airowl-iot/airowl/Firmware/squareline/projects/ui_square_line/cache/thumb_546388984Screenshot 2025-09-16 161635.png

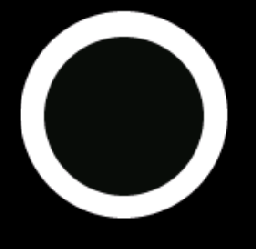
Firmware/squareline/projects/ui_square_line/cache/thumb_546388984Screenshot 2025-09-16 161635.png
