airowl-iot/airowl/Firmware/squareline/projects/ui_square_line/cache/thumb_812625368Glowing Blue Ring on Black.png

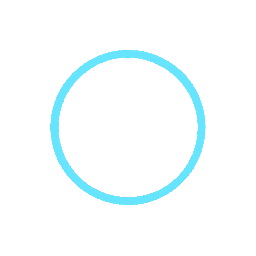
Firmware/squareline/projects/ui_square_line/cache/thumb_812625368Glowing Blue Ring on Black.png
