airowl-iot/airowl/Images/AIROWL edited renders and animation/n7.png

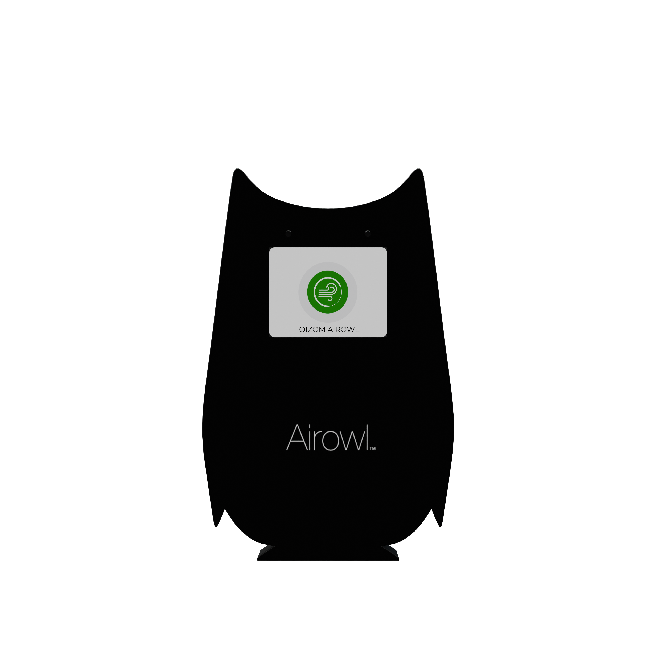
Images/AIROWL edited renders and animation/n7.png
