airowl-iot/airowl/Images/AIROWL edited renders and animation/n8.png

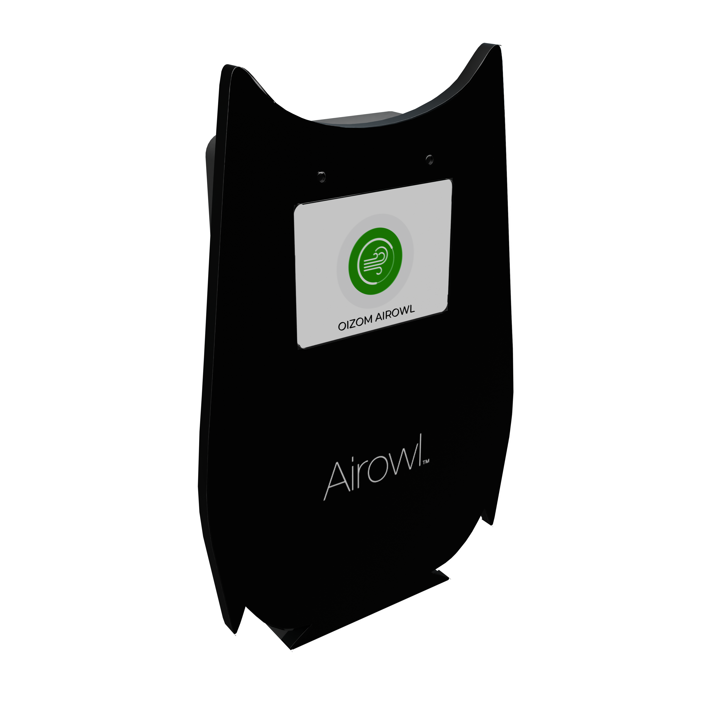
Images/AIROWL edited renders and animation/n8.png
