airowl-iot/airowl/Images/AIROWL edited renders and animation/n9.png

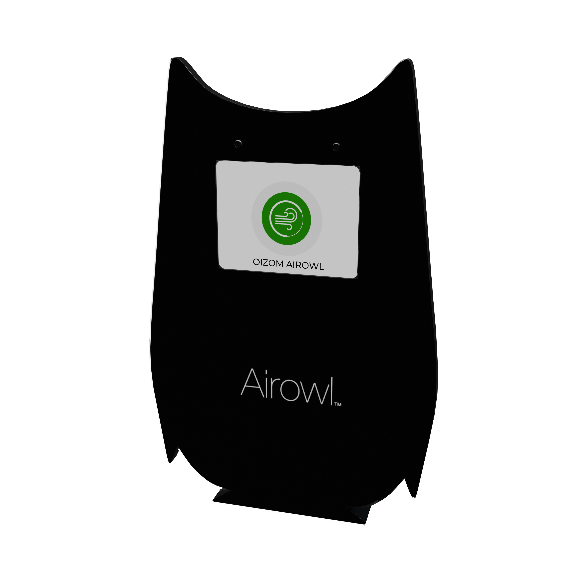
Images/AIROWL edited renders and animation/n9.png
