airowl-iot/airowl/Images/AIROWL edited renders and animation/n 1.n.png

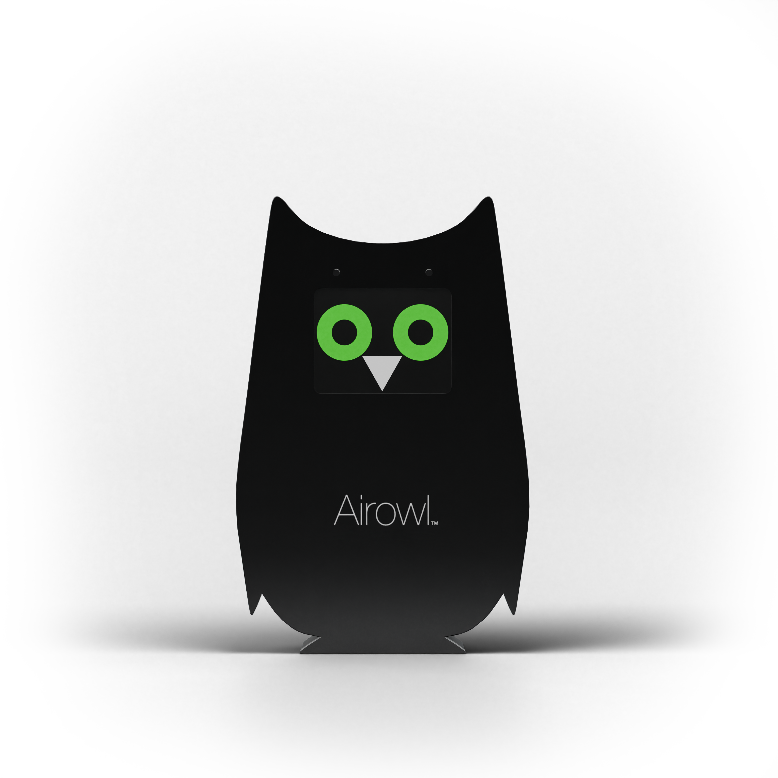
Images/AIROWL edited renders and animation/n 1.n.png
