airowl-iot/airowl/Images/AIROWL edited renders and animation/n 1.png

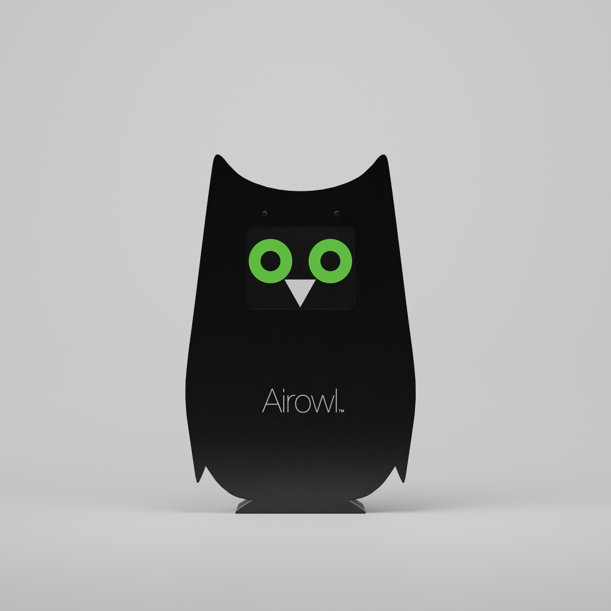
Images/AIROWL edited renders and animation/n 1.png
