airowl-iot/airowl/Images/AIROWL edited renders and animation/n 2.n.png

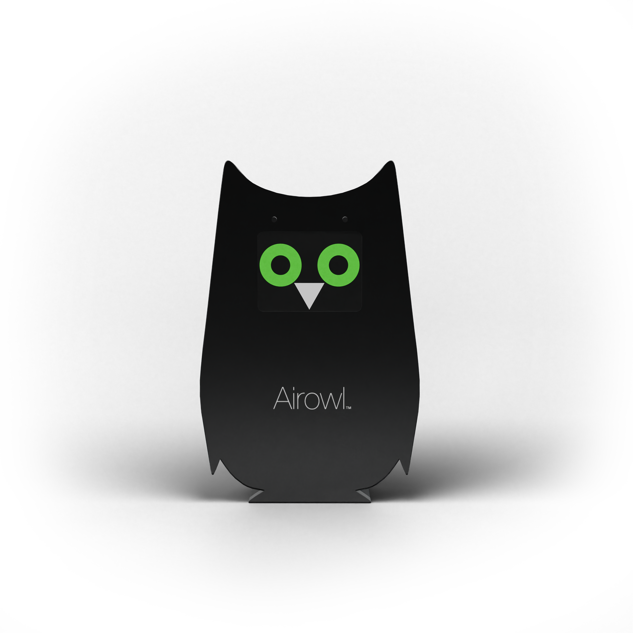
Images/AIROWL edited renders and animation/n 2.n.png
