airowl-iot/airowl/Images/AIROWL edited renders and animation/n 2e.png

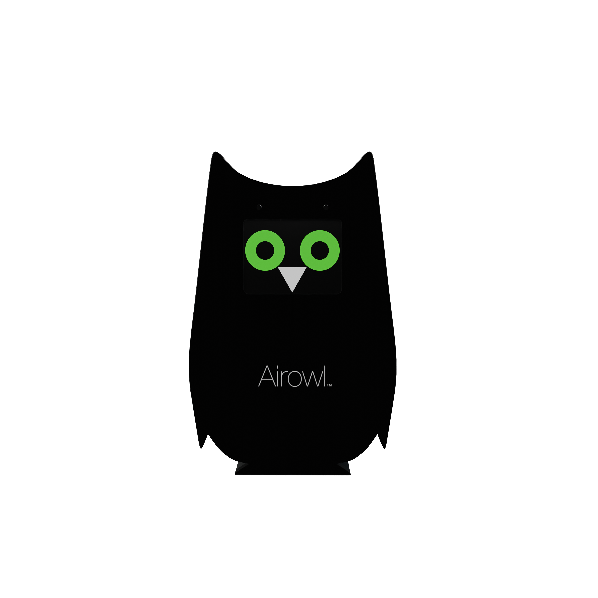
Images/AIROWL edited renders and animation/n 2e.png
