airowl-iot/airowl/Images/AIROWL edited renders and animation/n 3.n.png

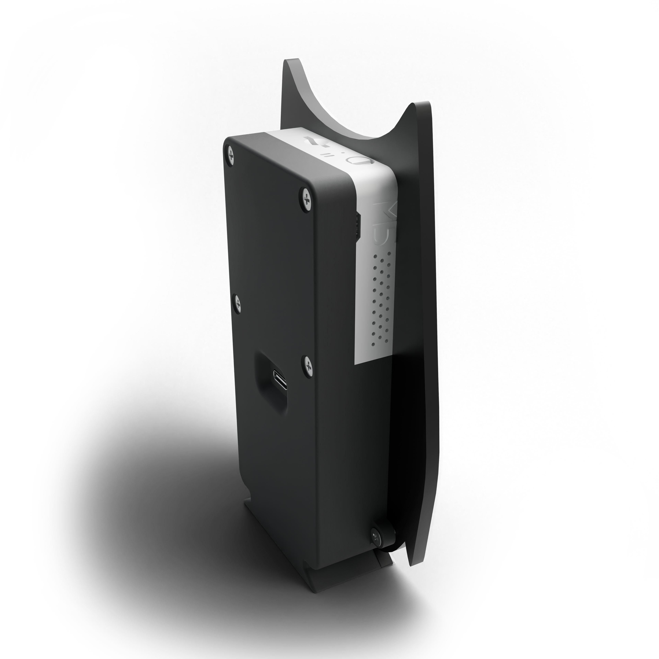
Images/AIROWL edited renders and animation/n 3.n.png
