airowl-iot/airowl/Images/AIROWL edited renders and animation/n 3e.png

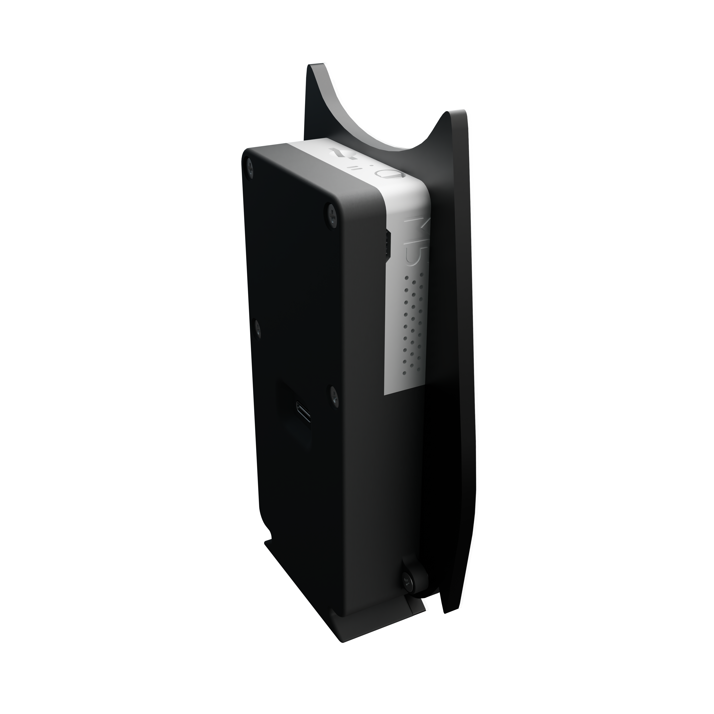
Images/AIROWL edited renders and animation/n 3e.png
