airowl-iot/airowl/Images/AIROWL edited renders and animation/n 4.n.png

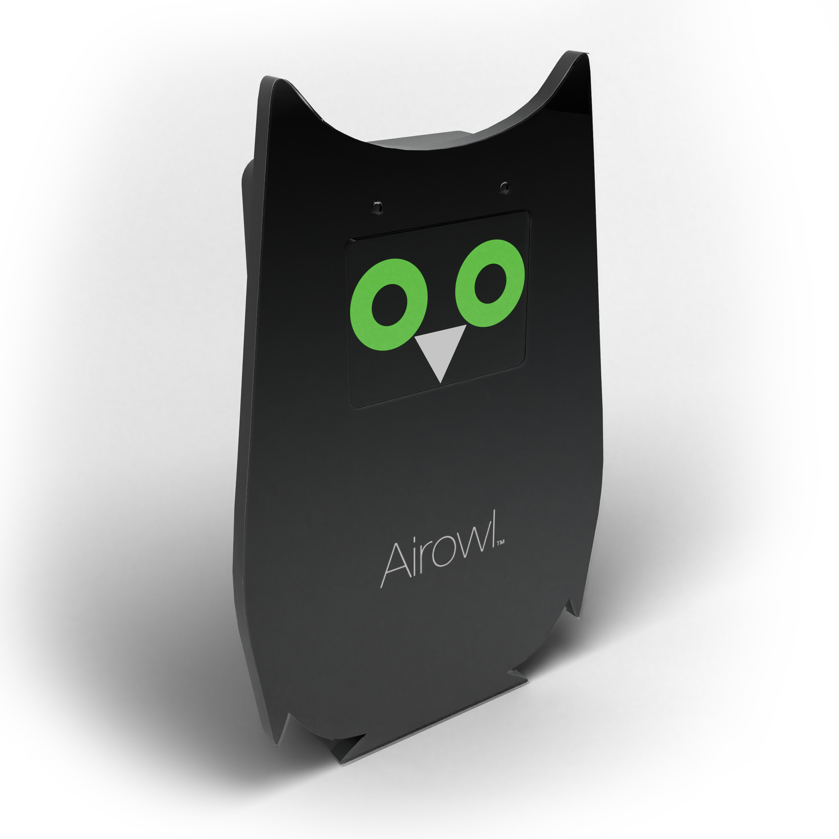
Images/AIROWL edited renders and animation/n 4.n.png
