airowl-iot/airowl/Images/AIROWL edited renders and animation/n 4.png

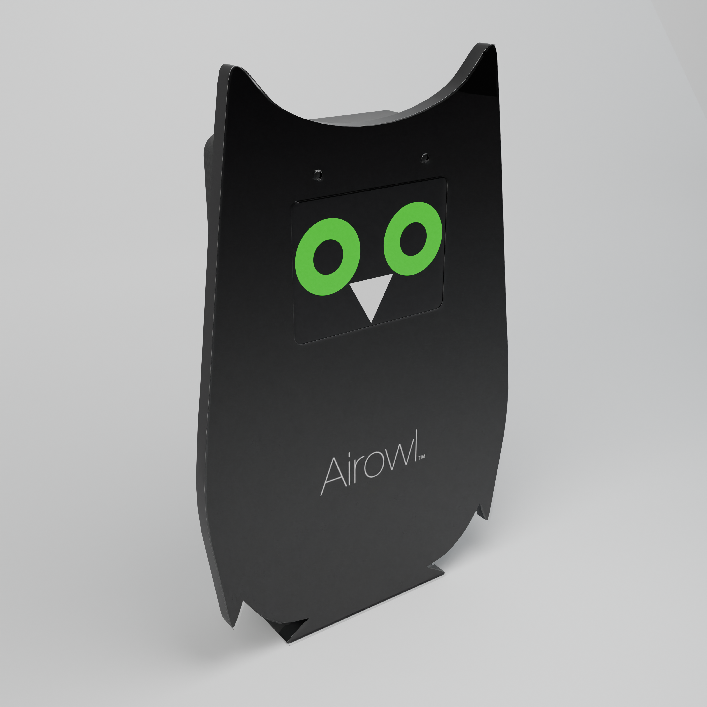
Images/AIROWL edited renders and animation/n 4.png
