airowl-iot/airowl/Images/AIROWL edited renders and animation/n 5.n.png

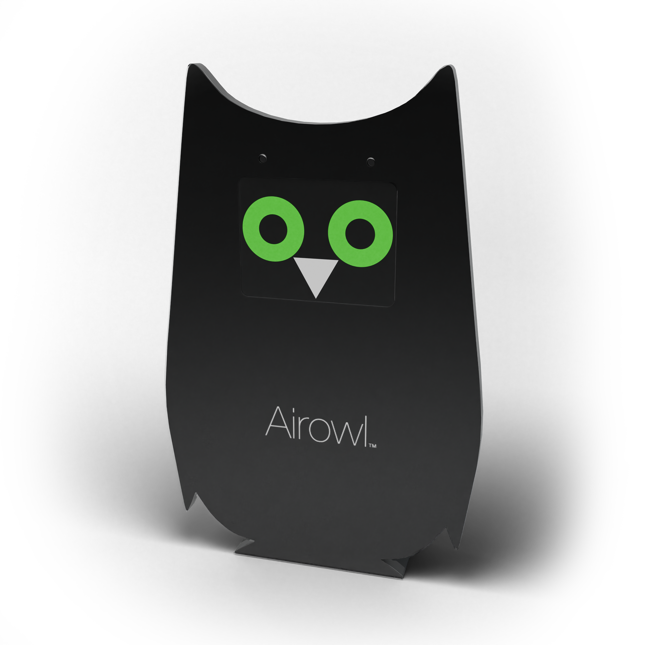
Images/AIROWL edited renders and animation/n 5.n.png
