airowl-iot/airowl/Images/AIROWL edited renders and animation/n 5.png

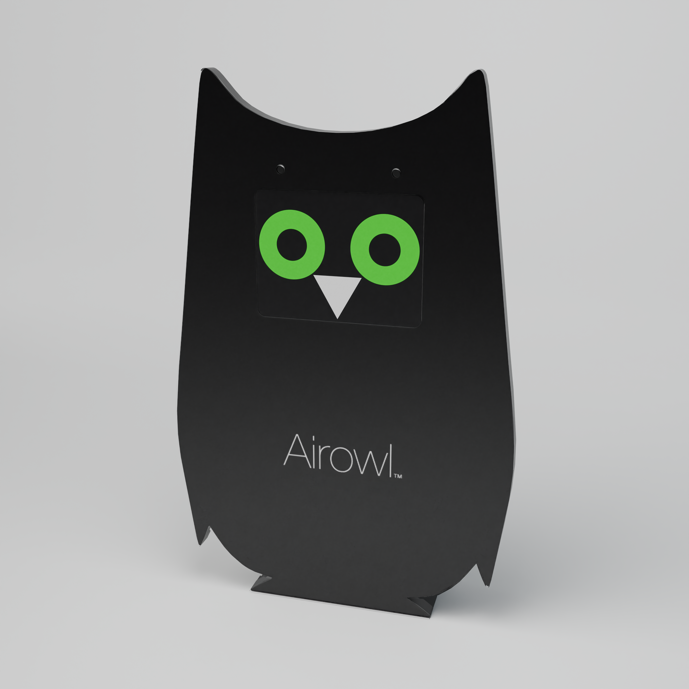
Images/AIROWL edited renders and animation/n 5.png
