airowl-iot/airowl/Images/AIROWL edited renders and animation/n 6.n.png

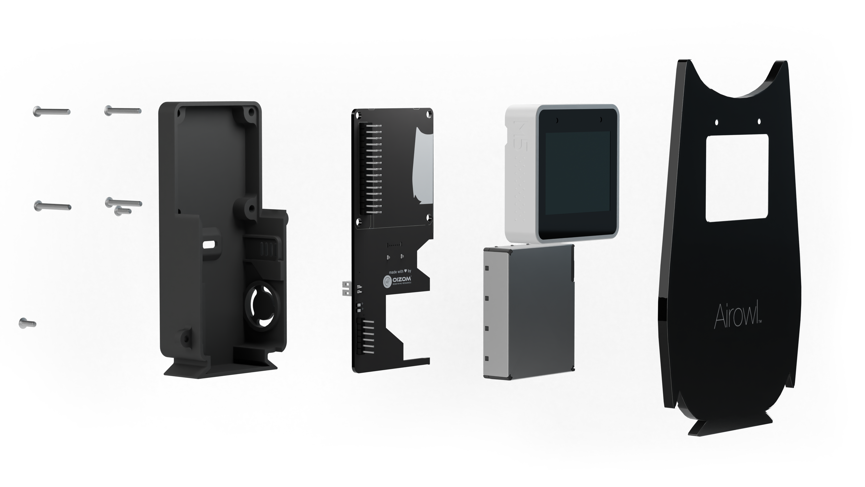
Images/AIROWL edited renders and animation/n 6.n.png
