airowl-iot/airowl/Images/AIROWL edited renders and animation/X1.png

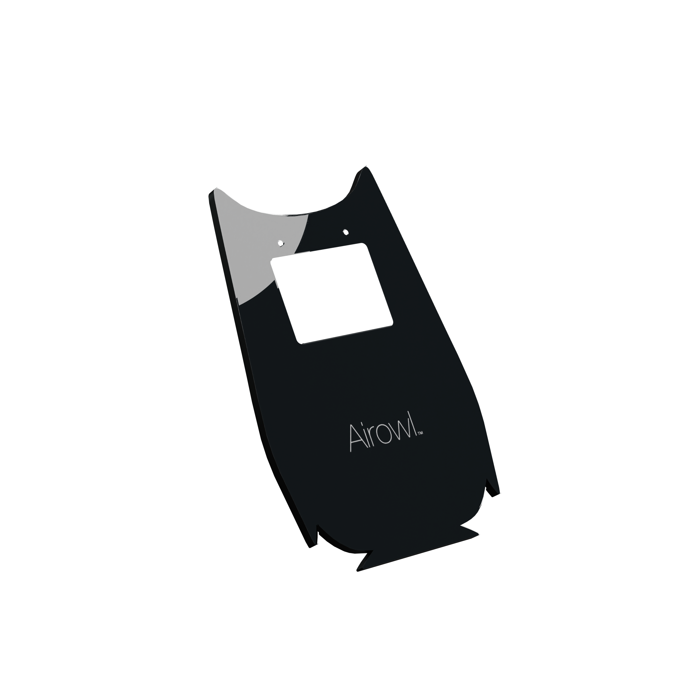
Images/AIROWL edited renders and animation/X1.png
