airowl-iot/airowl/Images/AIROWL edited renders and animation/x3.png

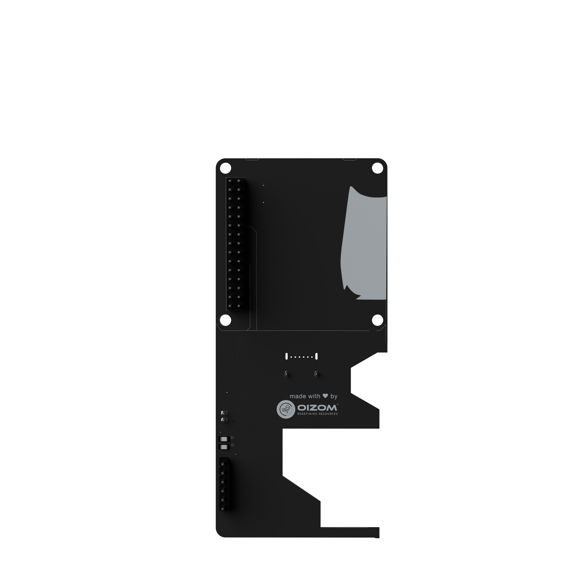
Images/AIROWL edited renders and animation/x3.png
