airowl-iot/airowl/Images/AIROWL edited renders and animation/x4.png

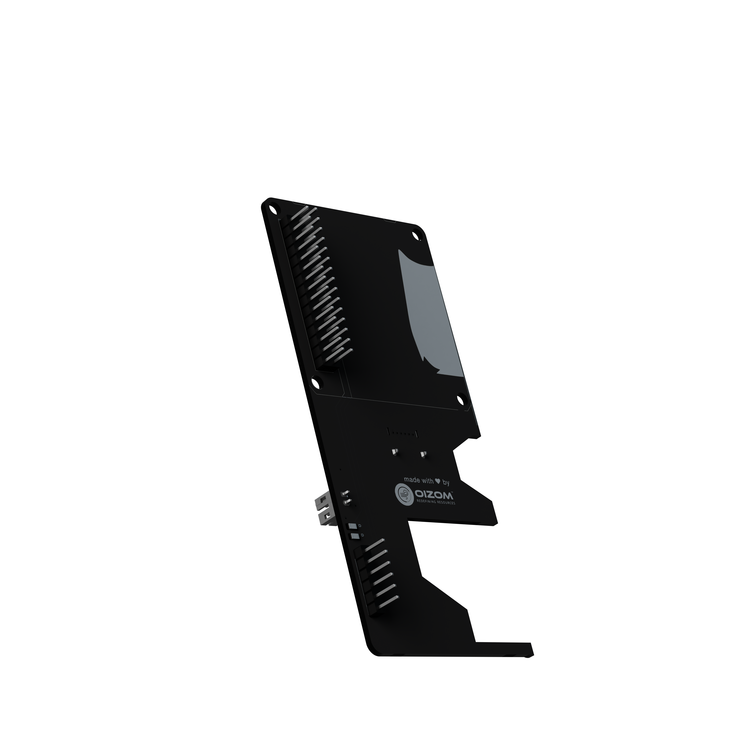
Images/AIROWL edited renders and animation/x4.png
