airowl-iot/airowl/Images/unnamed (1).png

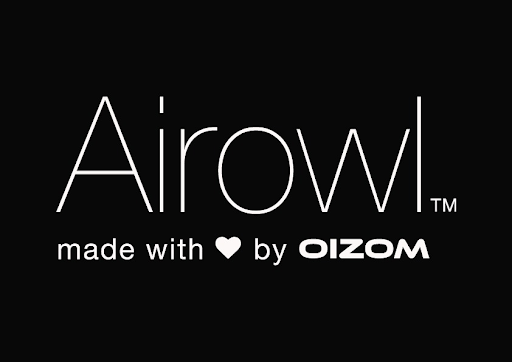
Images/unnamed (1).png
