airowl-iot/airowl/Firmware/src/service/ota_service.cpp

// ota_service.cpp - OTA Service for Airowl 3.0

#include "ota_service.h"
#include <WiFiClientSecure.h>
#include <HTTPClient.h>
#include <Update.h>
#include <ArduinoJson.h>
#include "airowl_config.h"
#include <esp_ota_ops.h>
#include <esp_task_wdt.h>
#include "hal/hal_wifi.h"
#include <WiFi.h>
#include <string.h>
#include "manager/config_manager.h"
#include "manager/sensor_manager.h"
#include "manager/event_manager.h"

#include "manager/ui_manager.h"

namespace {
    bool initialized = false;
    SVC::OTA::State currentState = SVC::OTA::State::IDLE;
    SVC::OTA::ProgressCallback progressCallback = nullptr;
    TaskHandle_t otaTaskHandle = nullptr;

    static bool tasksAreSuspended = false;
    static const int maxSuspendedTasks = 32;
    static TaskHandle_t suspendedTasks[maxSuspendedTasks];
    static int suspendedTaskCount = 0;

    String versionURL;
    String firmwareURL;

    // OTA delay mechanism
    static unsigned long wifiConnectedTime = 0;
    static bool otaCheckPending = false;
    static const unsigned long OTA_CHECK_DELAY_MS = 27000; 

    String fetchLatestVersion() {
        if (versionURL.isEmpty()) {
            auto* cfg = ConfigManager::getInstance();
            if (cfg && cfg->isInitialized()) {
                auto svcConfig = cfg->getServiceConfig("ota");
                if (svcConfig.params.count("versionURL")) {
                    versionURL = svcConfig.params.at("versionURL");
                }
            }

            if (versionURL.isEmpty()) {
                Serial.println("[OTA] ERROR: versionURL not configured in config.json");
                return "";
            }
        }

        Serial.printf("[OTA] Fetching version from: %s\n", versionURL.c_str());

        HTTPClient http;
        http.setFollowRedirects(HTTPC_STRICT_FOLLOW_REDIRECTS);
        if (!http.begin(versionURL.c_str())) {
            Serial.println("[OTA] http.begin() failed (version)");
            return "";
        }

        int httpCode = http.GET();
        if (httpCode != HTTP_CODE_OK) {
            Serial.printf("[OTA] Failed to fetch version info, code: %d\n", httpCode);
            http.end();
            return "";
        }

        String payload = http.getString();
        http.end();

        StaticJsonDocument<512> doc;
        if (deserializeJson(doc, payload)) {
            Serial.println("[OTA] JSON parse error");
            return "";
        }

        if (!doc.containsKey("version")) return "";

        String v = doc["version"].as<String>();
        v.trim();
        Serial.printf("[OTA] Latest version: %s\n", v.c_str());
        return v;
    }

    int versionToInt(const String& v) {
    int major = 0, minor = 0, patch = 0;
    sscanf(v.c_str(), "%d.%d.%d", &major, &minor, &patch);
    return major * 10000 + minor * 100 + patch;
    }

    bool isUpdateAvailable() {
        String latest = fetchLatestVersion();
        if (latest.isEmpty()) {
            Serial.println("[OTA] Failed to fetch latest version from server");
            return false;
        }

        String current = APP::UIController::FirmwareVersionLabel();
        if (current.isEmpty()) {
            Serial.println("[OTA] ERROR: UI firmware version label is empty or not set");
            return false;
        }

        current.trim();
        latest.trim();

        int currentVer = versionToInt(current);
        int latestVer  = versionToInt(latest);

         Serial.printf("[OTA] Version Compare → current=%d, latest=%d\n",
                  currentVer, latestVer);

    if (latestVer > currentVer) {
        Serial.printf("[OTA] Update available: %s → %s\n",
                      current.c_str(), latest.c_str());
        return true;
    }

    Serial.println("[OTA] No update needed (current version is newer)");
    return false;
}

    void updateState(SVC::OTA::State newState, int progress = -1, const char* message = nullptr) {
        const char* stateNames[] = {
            "IDLE", "CHECKING", "DOWNLOADING", "UPDATING", "SUCCESS", "FAILED"
        };

        Serial.printf("[OTA] State change: %s -> %s\n",
                      stateNames[(int)currentState], stateNames[(int)newState]);

        currentState = newState;

        if (progress >= 0) Serial.printf("[OTA] Progress: %d%%\n", progress);
        if (message) Serial.printf("[OTA] Message: %s\n", message);

        if (progressCallback) progressCallback(newState, progress, message ? message : "");

        if (newState == SVC::OTA::State::DOWNLOADING || newState == SVC::OTA::State::UPDATING) {
            if (progress >= 0) {
                auto event = std::make_shared<CORE::OTAProgressEvent>(progress, 100);
                CORE::EventBus::getInstance().publish(event);
            }
        } else if (newState == SVC::OTA::State::SUCCESS || newState == SVC::OTA::State::FAILED) {
            auto event = std::make_shared<CORE::OTACompleteEvent>(newState == SVC::OTA::State::SUCCESS);
            CORE::EventBus::getInstance().publish(event);
        }
    }

    bool downloadAndApplyFirmware(const String& initialUrl) {
        String url = initialUrl;
        const int MAX_REDIRECTS = 3;
        int redirects = 0;

        WiFiClient clientPlain;
        WiFiClientSecure clientSecure;
        clientSecure.setInsecure();

        while (redirects <= MAX_REDIRECTS) {
            HTTPClient http;
            bool secure = url.startsWith("https://");

            if (secure) {
                if (!http.begin(clientSecure, url)) {
                    Serial.printf("[OTA] http.begin() failed for %s\n", url.c_str());
                    http.end();
                    return false;
                }
            } else {
                if (!http.begin(clientPlain, url)) {
                    Serial.printf("[OTA] http.begin() failed for %s\n", url.c_str());
                    http.end();
                    return false;
                }
            }

            updateState(SVC::OTA::State::DOWNLOADING, 0, "Starting HTTP GET");
            int httpCode = http.GET();
            if (httpCode == HTTP_CODE_OK) {
                int contentLength = http.getSize();
                WiFiClient* stream = http.getStreamPtr();
                if (!stream) { http.end(); return false; }

                if (!Update.begin(contentLength > 0 ? contentLength : UPDATE_SIZE_UNKNOWN)) {
                    Serial.println("[OTA] Update.begin() failed");
                    http.end(); return false;
                }

                size_t written = Update.writeStream(*stream);
                Serial.printf("[OTA] Written %u bytes\n", (unsigned)written);

                if (!Update.end() || !Update.isFinished()) {
                    Serial.printf("[OTA] Update failed. Error: %d\n", Update.getError());
                    http.end(); return false;
                }

                Serial.println("[OTA] ✓ Update finished. Rebooting...");
                http.end();
                return true;
            } else if (httpCode == HTTP_CODE_MOVED_PERMANENTLY || httpCode == HTTP_CODE_FOUND || httpCode == HTTP_CODE_TEMPORARY_REDIRECT) {
                url = http.getLocation();
                if (url.length() == 0) return false;
                redirects++;
                http.end();
                continue;
            } else {
                Serial.printf("[OTA] HTTP GET failed, code: %d\n", httpCode);
                http.end();
                return false;
            }
        }
        Serial.println("[OTA] Too many redirects, aborting.");
        return false;
    }

} // namespace

namespace SVC {

bool OTA::otaInProgress = false;

bool OTA::init() {
    if (initialized) return true;
    Serial.println("[OTA] Initializing OTA service...");
    initialized = true;
    updateState(State::IDLE, 0, "OTA initialized");


    return true;
}

void OTA::setURLs(const char* versionUrl, const char* firmwareUrl) {
    if (versionUrl && strlen(versionUrl) > 0) {
        versionURL = versionUrl;
        Serial.printf("[OTA] Version URL set: %s\n", versionURL.c_str());
    }
    if (firmwareUrl && strlen(firmwareUrl) > 0) {
        firmwareURL = firmwareUrl;
        Serial.printf("[OTA] Firmware URL set: %s\n", firmwareURL.c_str());
    }
}

bool OTA::beginUpdate() {
    if (!initialized || otaInProgress) return false;

    if (firmwareURL.isEmpty()) {
        auto* cfg = ConfigManager::getInstance();
        if (cfg && cfg->isInitialized()) {
            auto svcConfig = cfg->getServiceConfig("ota");
            if (svcConfig.params.count("firmwareURL")) {
                firmwareURL = svcConfig.params.at("firmwareURL");
            }
        }

        if (firmwareURL.isEmpty()) {
            Serial.println("[OTA] ERROR: firmwareURL not configured in config.json");
            return false;
        }
    }

    Serial.printf("[OTA] Downloading firmware from: %s\n", firmwareURL.c_str());

    otaInProgress = true;
    updateState(State::DOWNLOADING, 0, "Preparing OTA");

    bool ok = downloadAndApplyFirmware(firmwareURL);
    if (!ok) {
        updateState(State::FAILED, 0, "OTA failed");
        otaInProgress = false;
        Serial.println("[OTA] ✗ Update failed!");
        return false;
    }

    updateState(State::SUCCESS, 100, "Update complete, rebooting");
    Serial.println("[OTA] ✓ Update successful!");
    Serial.println("[OTA] Rebooting ESP32 in 2 seconds...");
    Serial.flush();

    vTaskDelay(pdMS_TO_TICKS(2000));

    Serial.println("[OTA] Restarting NOW...");
    Serial.flush();

    ESP.restart();

    return true;
}

OTA::State OTA::getState() { return currentState; }

const char* OTA::getCurrentVersion() {
    static String versionStr;
    versionStr = APP::UIController::FirmwareVersionLabel();
    if (!versionStr.isEmpty()) {
        return versionStr.c_str();
    }
    Serial.println("[OTA] WARNING: UI firmware version label is empty");
    return "unknown";
}

void OTA::onProgress(ProgressCallback callback) { progressCallback = callback; }

void OTA::suspendOtherTasks() {
    if (tasksAreSuspended) return;

    Serial.println("[OTA] Suspending non-essential tasks...");
    suspendedTaskCount = 0;
    memset(suspendedTasks, 0, sizeof(suspendedTasks));

    TaskHandle_t sensorTask = APP::SensorManager::getTaskHandle();
    if (sensorTask && suspendedTaskCount < maxSuspendedTasks) {
        vTaskSuspend(sensorTask);
        suspendedTasks[suspendedTaskCount++] = sensorTask;
        Serial.println("[OTA] Sensor task suspended");
    }

    tasksAreSuspended = true;
    Serial.printf("[OTA] Total tasks suspended: %d (UI task kept alive for display)\n", suspendedTaskCount);
}

void OTA::resumeOtherTasks() {
    if (!tasksAreSuspended) {
        Serial.println("[OTA] No tasks to resume");
        return;
    }

    Serial.println("[OTA] Resuming suspended tasks...");
    for (int i = 0; i < suspendedTaskCount; ++i) {
        if (suspendedTasks[i]) {
            vTaskResume(suspendedTasks[i]);
            Serial.printf("[OTA] Resumed task %d\n", i);
        }
        suspendedTasks[i] = nullptr;
    }
    suspendedTaskCount = 0;
    tasksAreSuspended = false;
    Serial.println("[OTA] All tasks resumed");
}

void OTA::onWiFiConnected() {
    Serial.printf("[OTA] WiFi connected. Scheduling OTA check in %lu seconds...\n", OTA_CHECK_DELAY_MS / 1000);
    wifiConnectedTime = millis();
    otaCheckPending = true;
}

void OTA::loop() { /* empty */ }

void OTA::task(void* parameter) {
    Serial.println("[OTA] Task started");

    while(true) {
        if (otaCheckPending) {
            unsigned long elapsed = millis() - wifiConnectedTime;

            if (elapsed >= OTA_CHECK_DELAY_MS) {
                Serial.printf("[OTA] Delay complete (%lu seconds). Checking for updates...\n", elapsed / 1000);
                otaCheckPending = false;

                if (isUpdateAvailable()) {
                    Serial.println("[OTA] ✓ Update available! Starting OTA process...");

                    Serial.println("[OTA] Switching to OTA screen...");
                    APP::UIController::showOTAScreen();
                    vTaskDelay(pdMS_TO_TICKS(500)); 

                    Serial.println("[OTA] Suspending non-essential tasks...");
                    suspendOtherTasks();
                    vTaskDelay(pdMS_TO_TICKS(100));

                    Serial.println("[OTA] Starting firmware download...");
                    bool ok = beginUpdate();

                    if (!ok) {
                        Serial.println("[OTA] ✗ Update failed, resuming tasks...");
                        resumeOtherTasks();
                    }
                } else {
                    Serial.println("[OTA] No update available");
                }
            } else {
                static unsigned long lastCountdown = 0;
                if (millis() - lastCountdown >= 5000) {
                    unsigned long remaining = (OTA_CHECK_DELAY_MS - elapsed) / 1000;
                    Serial.printf("[OTA] Waiting %lu more seconds before checking for updates...\n", remaining);
                    lastCountdown = millis();
                }
            }
        }

        vTaskDelay(pdMS_TO_TICKS(1000));
    }
}

bool OTA::startTask() {
    if (otaTaskHandle) return true;
    return xTaskCreatePinnedToCore(task, "OTA", 8192, nullptr, 1, &otaTaskHandle, 0) == pdPASS;
}

bool OTA::restartTask() {
    if (otaTaskHandle) vTaskDelete(otaTaskHandle);
    otaTaskHandle = nullptr;
    return startTask();
}

} // namespace SVC
