airowl-iot/airowl/Firmware/src/manager/ui_manager.cpp

// ui_controller.cpp - UI Controller implementation for Airowl 3.0
#include "ui_manager.h"
#include "../hal/hal_display.h"
#include "../hal/hal_wifi.h"
#include "../service/mqtt_service.h"
#include <esp_task_wdt.h>
#include <time.h>
#include <esp_sntp.h>
#include "../service/ota_service.h"
#include "ui/ui_airowl/ui.h"
#include "manager/config_manager.h"
#include "sensor_manager.h"

namespace APP{

    struct ScreenMap {
    const char* name;
    lv_obj_t** screen;  // Changed to pointer-to-pointer
    };
    static ScreenMap screens[] = {
        {"dashboard", &ui_dashboard},
        {"intro", &ui_Intro},
        {"qrcode", &ui_qrcode},
        {"matter", &ui_matter},
        {"owl", &ui_owl},
        {"tempgraph", &ui_tempgraph},
        {"pm25graph", &ui_PM25graph},
        {"humdgraph", &ui_Humdgraph},
        {"pm10graph", &ui_PM10graph},
        {"tvocgraph", &ui_TVOCgraph},
        {"co2graph", &ui_eCO2graph},
        {"ota", &ui_ota}
    };
   
    bool initialized = false;
    bool running = false;
    bool otaInProgress = false;
    TaskHandle_t uiTaskHandle = nullptr;

    lv_obj_t* qrCodeObj = nullptr;
    String lastQRCodeUrl = "";
    String storedApName = ""; 

    uint32_t sensorReadingSubscriptionId = 0;
    uint32_t commandReceivedSubscriptionId = 0;
    uint32_t wifiStateSubscriptionId = 0;
    uint32_t otaProgressSubscriptionId = 0;

    static float lastPM25 = 0.0, lastPM10 = 0.0;
    static float lastTemp = 0.0, lastHumidity = 0.0;
    static float lastTVOC = 0.0, lastEco2 = 0.0;

    static void ui_event_WifiIcon(lv_event_t * e) { 
    if (lv_event_get_code(e) == LV_EVENT_CLICKED) {
        if (HAL::WiFi::getStatus() != HAL::WiFi::Status::CONNECTED) {
            _ui_screen_change(&ui_qrcode, LV_SCR_LOAD_ANIM_FADE_ON, 500, 0, &ui_qrcode_screen_init);
        }
    }   
}

    unsigned long bootTime = 0;
    const unsigned long EYE_COLOR_ACTIVATION_DELAY = 60000; 
    
    #define CHART_DATA_LENGTH 60  // Match history buffer size

    lv_chart_series_t *ui_PM25chart_series_1 = nullptr;
    static lv_coord_t ui_PM25chart_series_1_array[CHART_DATA_LENGTH] = {0};
    static float pm25_sum = 0.0;
    static int pm25_count = 0;

    lv_chart_series_t *ui_PM10chart_series_1 = nullptr;
    static lv_coord_t ui_PM10chart_series_1_array[CHART_DATA_LENGTH] = {0};
    static float pm10_sum = 0.0;
    static int pm10_count = 0;

      lv_chart_series_t *ui_Tempchart_series_1 = nullptr;
    static lv_coord_t ui_Tempchart_series_1_array[CHART_DATA_LENGTH] = {0};
    static float temp_sum = 0.0;
    static int temp_count = 0;

      lv_chart_series_t *ui_Humdchart_series_1 = nullptr;
    static lv_coord_t ui_Humdchart_series_1_array[CHART_DATA_LENGTH] = {0};
    static float humd_sum = 0.0;
    static int humd_count = 0;

      lv_chart_series_t *ui_Tvocchart_series_1 = nullptr;
    static lv_coord_t ui_Tvocchart_series_1_array[CHART_DATA_LENGTH] = {0};
    static float tvoc_sum = 0.0;
    static int tvoc_count = 0;

      lv_chart_series_t *ui_eCo2chart_series_1 = nullptr;
    static lv_coord_t ui_eCo2chart_series_1_array[CHART_DATA_LENGTH] = {0};
    static float eCo2_sum = 0.0;
    static int eCo2_count = 0;

    struct AQIBreakpoint {
        float low;
        float high;
        int aqiLow;
        int aqiHigh;
    };
    
    const AQIBreakpoint pm25Bps[] = {
        {0.0, 30.0, 0, 50},        // Good
        {31.0, 60.0, 51, 100},     // Satisfactory
        {61.0, 90.0, 101, 200},    // Moderate
        {91.0, 120.0, 201, 300},   // Poor
        {121.0, 250.0, 301, 400},  // Very Poor
        {251.0, 500.0, 401, 500}   // Severe
    };
    
    const AQIBreakpoint pm10Bps[] = {
        {0.0, 50.0, 0, 50},        // Good
        {51.0, 100.0, 51, 100},    // Satisfactory
        {101.0, 250.0, 101, 200},  // Moderate
        {251.0, 350.0, 201, 300},  // Poor
        {351.0, 430.0, 301, 400},  // Very Poor
        {431.0, 600.0, 401, 500}   // Severe
    };

    
    AQIBreakpoint getBreakpoint(float value, const AQIBreakpoint* breakpoints, int count) {
        for (int i = 0; i < count; i++) {
            if (value >= breakpoints[i].low && value <= breakpoints[i].high) {
                return breakpoints[i];
            }
        }
        return breakpoints[count - 1];
    }
    
    int calculateSubIndex(float value, const AQIBreakpoint& bp) {
        return (int)(
        ( (float)(bp.aqiHigh - bp.aqiLow) /
          (bp.high - bp.low) ) *
        (value - bp.low) +
        bp.aqiLow
    );
}
    
   void UIController::setupPM25Chart() {
        
        if (ui_Chart3 != nullptr) {
            lv_chart_set_type(ui_Chart3, LV_CHART_TYPE_LINE);
            lv_chart_set_point_count(ui_Chart3, CHART_DATA_LENGTH);
            lv_chart_set_range(ui_Chart3, LV_CHART_AXIS_PRIMARY_Y, 0, 100); 

            ui_PM25chart_series_1 = lv_chart_add_series(
                ui_Chart3, lv_color_hex(0x41b4d1), LV_CHART_AXIS_PRIMARY_Y);
            lv_chart_set_ext_y_array(ui_Chart3, ui_PM25chart_series_1,
                                   ui_PM25chart_series_1_array);

            for (int i = 0; i < CHART_DATA_LENGTH; i++) ui_PM25chart_series_1_array[i] = 0;

            Serial.println("[UIController] PM2.5 Chart initialized");
        }
        
    }
    
     void UIController::refreshPM25Chart() {

        if (ui_PM25chart_series_1 != nullptr && ui_Chart3 != nullptr) {
            // Get history data from SensorManager
            float history[CHART_DATA_LENGTH];
            int count = SensorManager::getPM25History(history, CHART_DATA_LENGTH);

            // Copy history to chart array
            for (int i = 0; i < CHART_DATA_LENGTH; i++) {
                if (i < count) {
                    ui_PM25chart_series_1_array[i] = (lv_coord_t)(history[i]);
                } else {
                    ui_PM25chart_series_1_array[i] = 0;
                }
            }

            // Calculate average from history
            if (count > 0) {
                float sum = 0;
                for (int i = 0; i < count; i++) {
                    sum += history[i];
                }
                float pm25_avg = sum / count;

                if (ui_pm25maxvalue != nullptr) {
                    char avgBuffer[8];
                    dtostrf(pm25_avg, 4, 1, avgBuffer);
                    lv_label_set_text(ui_pm25maxvalue, avgBuffer);
                }
            }

            lv_chart_refresh(ui_Chart3);
        }

    }
    
    void UIController::setupPM10Chart() {
        
        if (ui_pmChart != nullptr) {
            lv_chart_set_type(ui_pmChart, LV_CHART_TYPE_LINE);
            lv_chart_set_point_count(ui_pmChart, CHART_DATA_LENGTH);
            lv_chart_set_range(ui_pmChart, LV_CHART_AXIS_PRIMARY_Y, 0, 150); 

            ui_PM10chart_series_1 = lv_chart_add_series(
                ui_pmChart, lv_color_hex(0x41b4d1), LV_CHART_AXIS_PRIMARY_Y);
            lv_chart_set_ext_y_array(ui_pmChart, ui_PM10chart_series_1,
                                   ui_PM10chart_series_1_array);

           for (int i = 0; i < CHART_DATA_LENGTH; i++) ui_PM10chart_series_1_array[i] = 0;

        Serial.println("[UIController] PM10 Chart initialized");
    }
}

    void UIController::refreshPM10Chart() {

        if (ui_PM10chart_series_1 != nullptr && ui_pmChart != nullptr) {
            // Get history data from SensorManager
            float history[CHART_DATA_LENGTH];
            int count = SensorManager::getPM10History(history, CHART_DATA_LENGTH);

            // Copy history to chart array
            for (int i = 0; i < CHART_DATA_LENGTH; i++) {
                if (i < count) {
                    ui_PM10chart_series_1_array[i] = (lv_coord_t)(history[i]);
                } else {
                    ui_PM10chart_series_1_array[i] = 0;
                }
            }

            // Calculate average from history
            if (count > 0) {
                float sum = 0;
                for (int i = 0; i < count; i++) {
                    sum += history[i];
                }
                float pm10_avg = sum / count;

                if (ui_pm10maxvalue != nullptr) {
                    char avgBuffer[8];
                    dtostrf(pm10_avg, 4, 1, avgBuffer);
                    lv_label_set_text(ui_pm10maxvalue, avgBuffer);
                }
            }

            lv_chart_refresh(ui_pmChart);
        }

}

void UIController::setupTempChart() {
        
        if (ui_tempChart != nullptr) {
            lv_chart_set_type(ui_tempChart, LV_CHART_TYPE_LINE);
            lv_chart_set_point_count(ui_tempChart, CHART_DATA_LENGTH);
            lv_chart_set_range(ui_tempChart, LV_CHART_AXIS_PRIMARY_Y, 0, 50); 

            ui_Tempchart_series_1 = lv_chart_add_series(
                ui_tempChart, lv_color_hex(0x41b4d1), LV_CHART_AXIS_PRIMARY_Y);
            lv_chart_set_ext_y_array(ui_tempChart, ui_Tempchart_series_1,
                                   ui_Tempchart_series_1_array);

            for (int i = 0; i < CHART_DATA_LENGTH; i++) {
                ui_Tempchart_series_1_array[i] = 0;
            }
            
            Serial.println("[UIController] Temp Chart initialized");
        }
        
    }
    
    void UIController::refreshTempChart() {

        if (ui_Tempchart_series_1 != nullptr && ui_tempChart != nullptr) {

            float history[CHART_DATA_LENGTH];
            int count = SensorManager::getTempHistory(history, CHART_DATA_LENGTH);

            for (int i = 0; i < CHART_DATA_LENGTH; i++) {
                if (i < count) { 
                    ui_Tempchart_series_1_array[i] = (lv_coord_t)(history[i]);
                    } else {
                     ui_Tempchart_series_1_array[i] = 0;
                }
            }

             if (count > 0) {
                float sum = 0;
                for (int i = 0; i < count; i++) {
                    sum += history[i];
                }

            float temp_avg = sum / count;

            if (ui_tempgmaxvalue != nullptr) {
                char avgBuffer[8];
                dtostrf(temp_avg, 4, 1, avgBuffer);
                lv_label_set_text(ui_tempgmaxvalue, avgBuffer);
            }
        }
            lv_chart_refresh(ui_tempChart);
        }
    }

void UIController::setupHumdChart() {
        
        if (ui_Chart2  != nullptr) {
            lv_chart_set_type(ui_Chart2 , LV_CHART_TYPE_LINE);
            lv_chart_set_point_count(ui_Chart2 , CHART_DATA_LENGTH);
            lv_chart_set_range(ui_Chart2 , LV_CHART_AXIS_PRIMARY_Y, 0, 100); 

            ui_Humdchart_series_1 = lv_chart_add_series(
                ui_Chart2 , lv_color_hex(0x41b4d1), LV_CHART_AXIS_PRIMARY_Y);
            lv_chart_set_ext_y_array(ui_Chart2 , ui_Humdchart_series_1,
                                   ui_Humdchart_series_1_array);

            for (int i = 0; i < CHART_DATA_LENGTH; i++) {
                ui_Humdchart_series_1_array[i] = 0;
            }
            
            Serial.println("[UIController] Humd Chart initialized");
        }
        
    }
    
    void UIController::refreshHumdChart() {

        if (ui_Humdchart_series_1 != nullptr && ui_Chart2 != nullptr) {

            float history[CHART_DATA_LENGTH];
            int count = SensorManager::getHumdHistory(history, CHART_DATA_LENGTH);

            for (int i = 0; i < CHART_DATA_LENGTH; i++) {
                if (i < count) {
                ui_Humdchart_series_1_array[i] = (lv_coord_t)(history[i]);
                } else {
                    ui_Humdchart_series_1_array[i] = 0;
                }
            }

             if (count > 0) {
                float sum = 0;
                for (int i = 0; i < count; i++) {
                    sum += history[i];
                }
            float humd_avg = sum /count;

            if (ui_Humdmaxvalue1 != nullptr) {
                char avgBuffer[8];
                dtostrf(humd_avg, 4, 1, avgBuffer);
                lv_label_set_text(ui_Humdmaxvalue1, avgBuffer);
            }
        }
            lv_chart_refresh(ui_Chart2 );
        }
    }

void UIController::setupTvocChart() {
        
        if (ui_TVOCchart  != nullptr) {
            lv_chart_set_type(ui_TVOCchart , LV_CHART_TYPE_LINE);
            lv_chart_set_point_count(ui_TVOCchart , CHART_DATA_LENGTH);
            lv_chart_set_range(ui_TVOCchart , LV_CHART_AXIS_PRIMARY_Y, 0, 1000); 

            ui_Tvocchart_series_1 = lv_chart_add_series(
                ui_TVOCchart , lv_color_hex(0x41b4d1), LV_CHART_AXIS_PRIMARY_Y);
            lv_chart_set_ext_y_array(ui_TVOCchart , ui_Tvocchart_series_1,
                                   ui_Tvocchart_series_1_array);

            for (int i = 0; i < CHART_DATA_LENGTH; i++) {
                ui_Tvocchart_series_1_array[i] = 0;
            }
            
            Serial.println("[UIController] Tvoc Chart initialized");
        }
        
    }
    
 void UIController::refreshTvocChart() {

        if (ui_Tvocchart_series_1 != nullptr && ui_TVOCchart != nullptr) {
            // Get history data from SensorManager
            float history[CHART_DATA_LENGTH];
            int count = SensorManager::getTvocHistory(history, CHART_DATA_LENGTH);

            // Copy history to chart array
            for (int i = 0; i < CHART_DATA_LENGTH; i++) {
                if (i < count) {
                    ui_Tvocchart_series_1_array[i] = (lv_coord_t)(history[i]);
                } else {
                    ui_Tvocchart_series_1_array[i] = 0;
                }
            }

            // Calculate average from history
            if (count > 0) {
                float sum = 0;
                for (int i = 0; i < count; i++) {
                    sum += history[i];
                }
                float tvoc_avg = sum / count;

                if (ui_tvocmaxvalue != nullptr) {
                    char avgBuffer[8];
                    dtostrf(tvoc_avg, 4, 1, avgBuffer);
                    lv_label_set_text(ui_tvocmaxvalue, avgBuffer);
                }
            }

            lv_chart_refresh(ui_TVOCchart);
        }
    }

void UIController::setupeCo2Chart() {
        
        if (ui_eCO2chart  != nullptr) {
            lv_chart_set_type(ui_eCO2chart , LV_CHART_TYPE_LINE);
            lv_chart_set_point_count(ui_eCO2chart , CHART_DATA_LENGTH);
            lv_chart_set_range(ui_eCO2chart , LV_CHART_AXIS_PRIMARY_Y, 0, 4000); 

            ui_eCo2chart_series_1 = lv_chart_add_series(
                ui_eCO2chart , lv_color_hex(0x41b4d1), LV_CHART_AXIS_PRIMARY_Y);
            lv_chart_set_ext_y_array(ui_eCO2chart , ui_eCo2chart_series_1,
                                   ui_eCo2chart_series_1_array);

            for (int i = 0; i < CHART_DATA_LENGTH; i++) {
                ui_eCo2chart_series_1_array[i] = 0;
            }

            Serial.println("[UIController] eCO2 Chart initialized");
        }
        
    }
    
     void UIController::refresheCO2Chart() {

        if (ui_eCo2chart_series_1 != nullptr && ui_eCO2chart != nullptr) {
            // Get history data from SensorManager
            float history[CHART_DATA_LENGTH];
            int count = SensorManager::geteCo2History(history, CHART_DATA_LENGTH);

            // Copy history to chart array
            for (int i = 0; i < CHART_DATA_LENGTH; i++) {
                if (i < count) {
                    ui_eCo2chart_series_1_array[i] = (lv_coord_t)(history[i]);
                } else {
                    ui_eCo2chart_series_1_array[i] = 0;
                }
            }

            // Calculate average from history
            if (count > 0) {
                float sum = 0;
                for (int i = 0; i < count; i++) {
                    sum += history[i];
                }
                float eCo2_avg = sum / count;

                if (ui_eco2max2 != nullptr) {
                    char avgBuffer[8];
                    dtostrf(eCo2_avg, 4, 1, avgBuffer);
                    lv_label_set_text(ui_eco2max2, avgBuffer);
                }
            }

            lv_chart_refresh(ui_eCO2chart);
        }
    }

void UIController::showOTAScreen() {
    Serial.println("[UIController] OTA mode activated - freezing UI updates");

    // Set flag FIRST to prevent any further UI updates
    otaInProgress = true;

    // Delete all LVGL animations to stop scheduled screen transitions
    lv_anim_del_all();
    Serial.println("[UIController] Cleared all LVGL animations");

    if (ui_ota != nullptr) {
        // Load OTA screen immediately without animation
        lv_scr_load(ui_ota);
        Serial.println("[UIController] Switched to OTA screen (locked)");
    } else {
        Serial.println("[UIController] ERROR: ui_ota is NULL!");
    }
}

bool UIController::init() {
    if (initialized) {
        Serial.println("[UIController] Already initialized, returning true");
        return true;
    }

    Serial.println("[UIController] Starting initialization...");
    
    bootTime = millis();
    configTime(19800, 0, "pool.ntp.org", "time.nist.gov"); 
    Serial.println("[UIController] NTP time synchronization started");
    
    Serial.println("[UIController] Initializing display...");
    if (!HAL::Display::init()) {
        Serial.println("[UIController] Display/LVGL init failed!");
        return false;
    }
    
    ui_Intro_screen_init();
    ui_qrcode_screen_init();
    ui_matter_screen_init();
    ui_owl_screen_init();
    ui_dashboard_screen_init();
    ui_Tempgraph_screen_init();
    ui_Humdgraph_screen_init();
    ui_PM25graph_screen_init();
    ui_PM10graph_screen_init();
    ui_TVOCgraph_screen_init();
    ui_eCO2graph_screen_init();
    ui_ota_screen_init();
    Serial.println("[UIController] All UI screens initialized");

    setupPM25Chart();
    setupPM10Chart();
    setupTempChart();
    setupHumdChart();
    setupTvocChart();
    setupeCo2Chart();

    if (ui_Intro != nullptr) {
        lv_disp_load_scr(ui_Intro);
        Serial.println("[UIController] Loaded intro screen");
    } else {
        Serial.println("[UIController] ERROR: ui_Intro is NULL!");
    }

    CORE::EventBus& eventBus = CORE::EventBus::getInstance();
    
    sensorReadingSubscriptionId = eventBus.subscribe(
        CORE::Event::Type::SENSOR_READING,
        handleSensorReadingEvent
    );
    
    commandReceivedSubscriptionId = eventBus.subscribe(
        CORE::Event::Type::COMMAND_RECEIVED,
        handleCommandReceivedEvent
    );

    wifiStateSubscriptionId = eventBus.subscribe(
        CORE::Event::Type::WIFI_STATE_CHANGED,
        [](const std::shared_ptr<const CORE::Event>& event) {
            auto wifiEvent = std::static_pointer_cast<const CORE::WiFiStateChangedEvent>(event);
            Serial.printf("[UIController] WiFi state changed: %d, SSID: %s, RSSI: %d\n",
                          (int)wifiEvent->getState(), wifiEvent->getSSID().c_str(), wifiEvent->getRSSI());
            UIController::updateWiFiStatus(); 
        }
    );

    otaProgressSubscriptionId = eventBus.subscribe(
        CORE::Event::Type::OTA_PROGRESS,
        [](const std::shared_ptr<const CORE::Event>& event) {
            auto otaEvent = std::static_pointer_cast<const CORE::OTAProgressEvent>(event);
            Serial.printf("[UIController] OTA Progress: %zu/%zu bytes\n",
                          otaEvent->getWritten(), otaEvent->getTotal());
        }
    );

    Serial.println("[UIController] Event subscriptions registered");
    Serial.printf("[UIController] Subscriptions - Sensor:%u, Command:%u, WiFi:%u, MQTT:%u, OTA:%u\n",
                  sensorReadingSubscriptionId, commandReceivedSubscriptionId,
                  wifiStateSubscriptionId, otaProgressSubscriptionId);

    SVC::OTA::onProgress([](SVC::OTA::State state, int progress, const char* message) {
    Serial.printf("[UIController][OTA] State=%d, Progress=%d, Msg=%s\n", (int)state, progress, message);

    if (state == SVC::OTA::State::DOWNLOADING || state == SVC::OTA::State::UPDATING) {
        APP::UIController::showOTAScreen();
    }
});

    initialized = true;
    running = true;

    bool taskStarted = startTask();
    Serial.printf("[UIController] Task creation %s\n", taskStarted ? "SUCCESS" : "FAILED");
    return taskStarted;
}

bool UIController::restartTask() {
    if (uiTaskHandle != nullptr) {
        TaskHandle_t tempHandle = uiTaskHandle;
        uiTaskHandle = nullptr;  
        vTaskDelete(tempHandle);
        vTaskDelay(pdMS_TO_TICKS(100)); 
        Serial.println("[UIController] Task deleted, restarting...");
    }
    return startTask();
}

void UIController::stop() {
    running = false;
}

bool UIController::isRunning() {
    return running;
}

bool UIController::switchScreen(const char* screenName) {
    Serial.printf("[UIController] switchScreen called with: '%s'\n", screenName);

    for (auto& s : screens) {
        lv_obj_t* screenPtr = s.screen ? *s.screen : nullptr;
        Serial.printf("[UIController] Checking screen: '%s', ptr: %p\n", s.name, screenPtr);

        if (strcmp(s.name, screenName) == 0) {
            if (screenPtr != nullptr) {
                Serial.printf("[UIController] Screen found and valid, loading...\n");
                lv_scr_load(screenPtr);

                if (strcmp(screenName, "qrcode") == 0) {
                    updateQRCode();
                }

                return true;
            } else {
                Serial.printf("[UIController] Screen found but screen pointer is NULL!\n");
                return false;
            }
        }
    }

    Serial.printf("[UIController] Screen '%s' not found in screens array\n", screenName);
    return false;
}

void UIController::updateSensorDisplay(CORE::SensorReadingEvent::SensorType sensorType,
                                       const std::vector<float>& values) {
    if (!running || values.empty()) {
        Serial.printf("[UIController] updateSensorDisplay skipped - running:%d, values:%zu\n",
                      running, values.size());
        return;
    }

    if (otaInProgress) {
        return;
    }

    // Serial.printf("[UIController] updateSensorDisplay called - type:%d, values:%zu\n",
    //               (int)sensorType, values.size());
    
    switch (sensorType) {
        case CORE::SensorReadingEvent::SensorType::PM700:
            if (values.size() >= 4) {
                
                char  pm25buffer[16], pm10buffer[16];
                dtostrf(values[0], 6, 1, pm25buffer); 
                dtostrf(values[1], 6, 1, pm10buffer);
                
                lv_label_set_text(ui_pm25value, pm25buffer);
                lv_label_set_text(ui_pm10value, pm10buffer);

                // Note: Charts now refresh from history buffer, not live data
                lastPM25 = values[0];
                lastPM10 = values[1];

                updateSensorColors(values.data());
                
            }
            break;
            
        case CORE::SensorReadingEvent::SensorType::AHT:
            if (values.size() >= 4) {
                
                char tempbuffer[16];
                char humbuffer[16]; 
                char tvocbuffer[16];
                char eco2buffer[16];   

                dtostrf(values[0], 4, 1, tempbuffer);
                dtostrf(values[1], 4, 1, humbuffer);
                dtostrf(values[2], 4, 1, tvocbuffer);
                dtostrf(values[3], 4, 1, eco2buffer);

                lv_label_set_text(ui_tempvalue, tempbuffer);
                lv_label_set_text(ui_humdvalue, humbuffer);
                lv_label_set_text(ui_tvocvalue, tvocbuffer);
                lv_label_set_text(ui_eCO2value, eco2buffer);

                lastTemp = values[0];
                lastHumidity = values[1];
                lastTVOC =  values[2];
                lastEco2 =  values[3];

                Serial.printf("[UIController] Updated display - T:%.1f°C, H:%.1f%%, TVOC:%d ppb, eCO2:%d ppm\n",
                              values[0], values[1], (int)values[2], (int)values[3]);
            }
            break;
        default:
            break;
    }
}

void UIController::updateWiFiStatus() {
    if (!running) return;

    bool isConnected = (HAL::WiFi::getStatus() == HAL::WiFi::Status::CONNECTED);

    if (ui_nose != nullptr) {
        if (isConnected) {
            lv_img_set_src(ui_nose, &ui_img_airowl_2_png);  
        } else {
            lv_img_set_src(ui_nose, &ui_img_airowl_1_png);  
        }
    }

    if (ui_wifi != nullptr) {
        if (isConnected) {
            lv_img_set_src(ui_wifi, &ui_img_wifi_on_png);
            lv_obj_remove_event_cb(ui_wifi, ui_event_WifiIcon);
            lv_obj_clear_flag(ui_wifi, LV_OBJ_FLAG_CLICKABLE);
        } else {
            lv_img_set_src(ui_wifi, &ui_img_wifi_off_png);
            lv_obj_add_event_cb(ui_wifi, ui_event_WifiIcon, LV_EVENT_CLICKED, nullptr);
            lv_obj_add_flag(ui_wifi, LV_OBJ_FLAG_CLICKABLE);
        }
    }

    if (ui_IPlabel != nullptr) {
        if (isConnected) {
            HAL::WiFi::ConnectionInfo info;
            if (HAL::WiFi::getConnectionInfo(&info)) {
                lv_label_set_text(ui_IPlabel, info.ip.toString().c_str());
            } else {
                lv_label_set_text(ui_IPlabel, "--");
            }
        } else {
            lv_label_set_text(ui_IPlabel, "--");
        }
    }

}

void UIController::updateQRCode() {
    if (!running || !ui_qrcode) return;

    String apName = storedApName.isEmpty() ? HAL::WiFi::generateApName() : storedApName;
    String qrcodeurl = (HAL::WiFi::getStatus() == HAL::WiFi::Status::CONNECTED) 
        ? "https://opendata.oizom.com/device/" + apName 
        : "WIFI:T:WPA;S:" + apName + ";P:12345678;;";

    // Serial.printf("[UIController] QR Code URL: %s\n", qrcodeurl.c_str());
    
    if (qrcodeurl != lastQRCodeUrl || qrCodeObj == nullptr) {

        if (qrCodeObj == nullptr) {
            qrCodeObj = lv_qrcode_create(ui_qrcode, 150, lv_color_black(), lv_color_white());
            lv_obj_center(qrCodeObj);
        }
        
        lv_qrcode_update(qrCodeObj, qrcodeurl.c_str(), qrcodeurl.length());
        lv_obj_center(qrCodeObj);

        lastQRCodeUrl = qrcodeurl;
        Serial.printf("[UIController] UI labels initialized with AP name: %s\n", apName);
        
    }
        lv_label_set_text(ui_devicename, apName.c_str());
        lv_label_set_text(ui_qrcodename, apName.c_str());
        // lv_label_set_text(ui_firmwareversion, "4.0.0");  
        
}

void UIController::updateSensorColors(const float* pmValues) {
    if (!running) return;
    
    AQIBreakpoint pm25Bp = getBreakpoint(pmValues[0], pm25Bps, sizeof(pm25Bps) / sizeof(pm25Bps[0]));
    AQIBreakpoint pm10Bp = getBreakpoint(pmValues[1], pm10Bps, sizeof(pm10Bps) / sizeof(pm10Bps[0]));

    int pm25Index = calculateSubIndex(pmValues[0], pm25Bp);
    int pm10Index = calculateSubIndex(pmValues[1], pm10Bp);
    uint32_t  pm25_color, pm10_color;

    if (millis() - bootTime < EYE_COLOR_ACTIVATION_DELAY) {
       pm25_color = pm10_color =  0xFFFFFF; 
    } else {
        pm25_color = getAQIColor(pm25Index);
        pm10_color = getAQIColor(pm10Index);
    }
    lv_obj_set_style_text_color(ui_pm25value, lv_color_hex(pm25_color), LV_PART_MAIN | LV_STATE_DEFAULT);
    lv_obj_set_style_text_color(ui_pm10value, lv_color_hex(pm10_color), LV_PART_MAIN | LV_STATE_DEFAULT);

    int overallAQI = max(pm25Index, pm10Index);
    uint32_t eyeColor = (millis() - bootTime < EYE_COLOR_ACTIVATION_DELAY) ? 0xFFFFFF : getAQIColor(overallAQI);
    updateEyeColors(eyeColor);
    
}

void UIController::updateEyeColors(uint32_t color) {
    if (ui_lefteye && ui_righteye) {
        lv_obj_set_style_bg_color(ui_lefteye, lv_color_hex(color), LV_PART_MAIN | LV_STATE_DEFAULT);
        lv_obj_set_style_bg_color(ui_righteye, lv_color_hex(color), LV_PART_MAIN | LV_STATE_DEFAULT);
    }
    
}

uint32_t UIController::getAQIColor(int aqi) {
        if (aqi <= 50)       return 0x009966; // Good (Green)
        else if (aqi <= 100) return 0x66CC66; // Satisfactory (Light Green)
        else if (aqi <= 200) return 0xFFDE33; // Moderate (Yellow)
        else if (aqi <= 300) return 0xFF9933; // Poor (Orange)
        else if (aqi <= 400) return 0xCC0033; // Very Poor (Red)
        else                 return 0x660099; // Severe (Maroon)
    }


void UIController::updateTimeDisplay() {
    if (!running || !ui_time) return;
    
    time_t now = time(nullptr);
    if (now > 0) { 
        struct tm timeinfo;
        localtime_r(&now, &timeinfo);
        char timeStr[9];
        strftime(timeStr, sizeof(timeStr), "%H:%M:%S", &timeinfo);
        lv_label_set_text(ui_time, timeStr);

        if (ui_date) {
            char dateStr[20];
            strftime(dateStr, sizeof(dateStr), "%d-%m", &timeinfo);  
            lv_label_set_text(ui_date, dateStr);
        }
    } else {
        unsigned long uptime = millis() / 1000;
        unsigned long hours = (uptime / 3600) % 24;
        unsigned long minutes = (uptime % 3600) / 60;
        unsigned long seconds = uptime % 60;
        char uptimeStr[9];
        snprintf(uptimeStr, sizeof(uptimeStr), "%02lu:%02lu:%02lu", hours, minutes, seconds);
        lv_label_set_text(ui_time, uptimeStr);

        if (ui_date) {
            lv_label_set_text(ui_date, "--");
        }
    }
    
}

void UIController::handleSensorReadingEvent(const std::shared_ptr<const CORE::Event>& event) {
    // Serial.println("[UIController] SensorReadingEvent received");
    auto sensorEvent = std::static_pointer_cast<const CORE::SensorReadingEvent>(event);
    auto readings = sensorEvent->getReadings();
    // Serial.printf("[UIController] Sensor type: %d, Reading count: %zu\n",
    //               (int)sensorEvent->getSensor(), readings.size());
    if (!readings.empty()) {
        // Serial.printf("[UIController] First value: %.2f\n", readings[0]);
    }
    updateSensorDisplay(sensorEvent->getSensor(), sensorEvent->getReadings());
}

void UIController::handleCommandReceivedEvent(const std::shared_ptr<const CORE::Event>& event) {
    auto cmdEvent = std::static_pointer_cast<const CORE::CommandReceivedEvent>(event);
    const String& command = cmdEvent->getCommand();
    const String& payload = cmdEvent->getPayload();

    if (command == "screen" && payload.length() > 0) {
        switchScreen(payload.c_str());
    }
}

void UIController::task(void* parameter) {
    esp_task_wdt_add(NULL);

    Serial.println("[UIController] Task started");
    static unsigned long lastDebugLog = 0;

    while (true) {
        esp_task_wdt_reset();

        if (running) {
            esp_task_wdt_reset();
            HAL::Display::lvHandler();  
            esp_task_wdt_reset();

            if (otaInProgress) {
                vTaskDelay(pdMS_TO_TICKS(50));  
                continue;
            }

            if (millis() - lastDebugLog >= 5000) {
                // Serial.printf("[UIController] Task running - PM2.5:%.1f, Temp:%.1f°C\n",
                //              lastPM25, lastTemp);
                lastDebugLog = millis();
            }

            static unsigned long lastWiFiUpdate = 0;
            if (millis() - lastWiFiUpdate >= 1000) {
                updateWiFiStatus();
                updateQRCode();
                updateTimeDisplay();
                lastWiFiUpdate = millis();
            }
        }
        vTaskDelay(pdMS_TO_TICKS(10));
    }
}

bool UIController::startTask() {
    if (uiTaskHandle != nullptr) {
        return true;
    }

    BaseType_t result = xTaskCreatePinnedToCore(
        task,
        "UIController",
        8192,
        NULL,
        2,
        &uiTaskHandle,
        1
    );

    return (result == pdPASS);
}

String UIController::FirmwareVersionLabel() {
    if (ui_firmwareversion == nullptr) {
        Serial.println("[UIController] ERROR: ui_firmwareversion label is NULL");
        return "";
    }

    const char* labelText = lv_label_get_text(ui_firmwareversion);
    if (labelText == nullptr) {
        Serial.println("[UIController] ERROR: ui_firmwareversion label text is NULL");
        return "";
    }

    String version = String(labelText);

    // Remove "Version-" or "Version- " prefix if present
    if (version.startsWith("Version-")) {
        version = version.substring(8);
    } else if (version.startsWith("Version- ")) {
        version = version.substring(9);
    }

    version.trim();
    Serial.printf("[UIController] Current firmware version from UI label: '%s'\n", version.c_str());
    return version;
}

TaskHandle_t UIController::getTaskHandle() {
    return uiTaskHandle;
}

} // namespace APP

// C-compatible helper functions for use in .c files
extern "C" {
    bool isWiFiConnected(void) {
        return HAL::WiFi::getStatus() == HAL::WiFi::Status::CONNECTED;
    }

    bool isMatterEnabled(void) {
        // ConfigManager is singleton in global namespace
        ServiceConfig cfg = ConfigManager::getInstance()->getServiceConfig("matter");
        return cfg.enabled;
    }

    void debugLog(const char* msg) {
        Serial.println(msg);
    }
}
